cristianoag/minimig/case/Acrylic/minimig_top_engraving.png

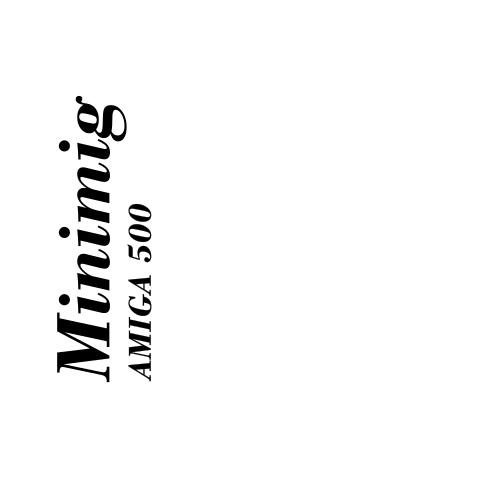
case/Acrylic/minimig_top_engraving.png
