cristianoag/minimig/pictures/20221220_040925518_iOS (Medium).jpg

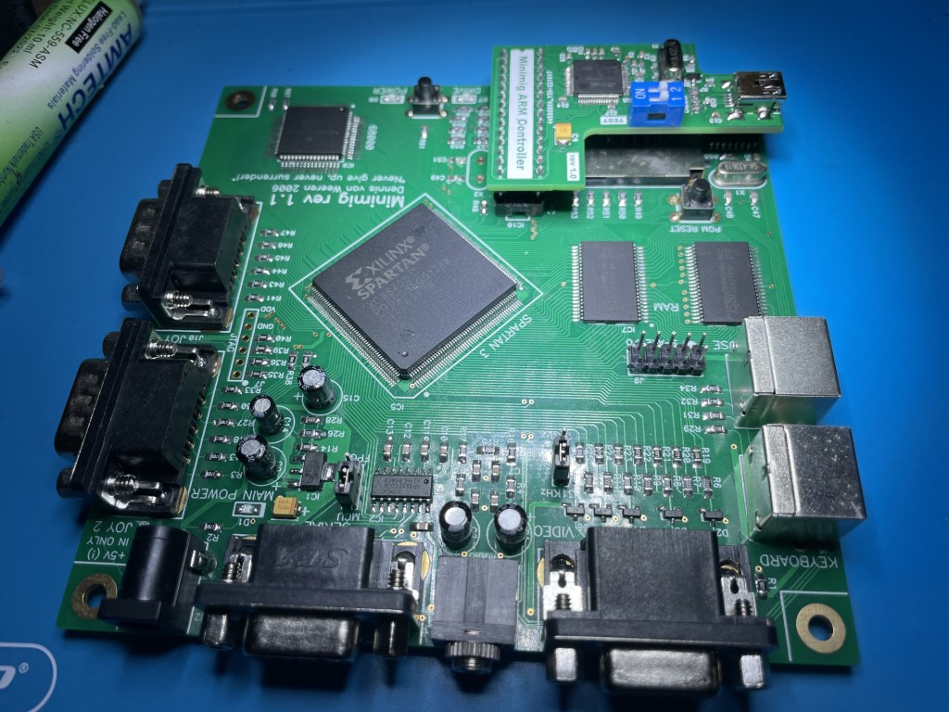
pictures/20221220_040925518_iOS (Medium).jpg
