cristianoag/minimig/pictures/20221222_223349225_iOS.jpg

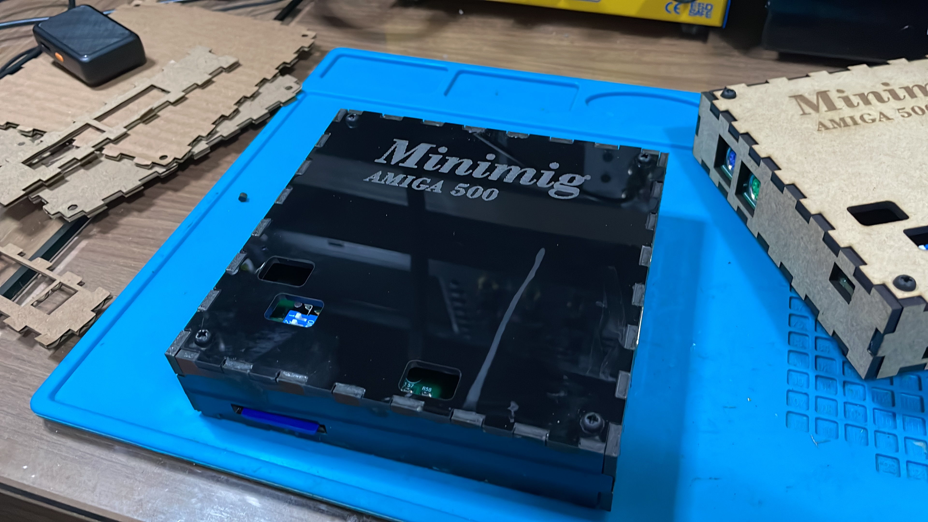
pictures/20221222_223349225_iOS.jpg
