cristianoag/minimig/pictures/20221222_223627648_iOS.jpg

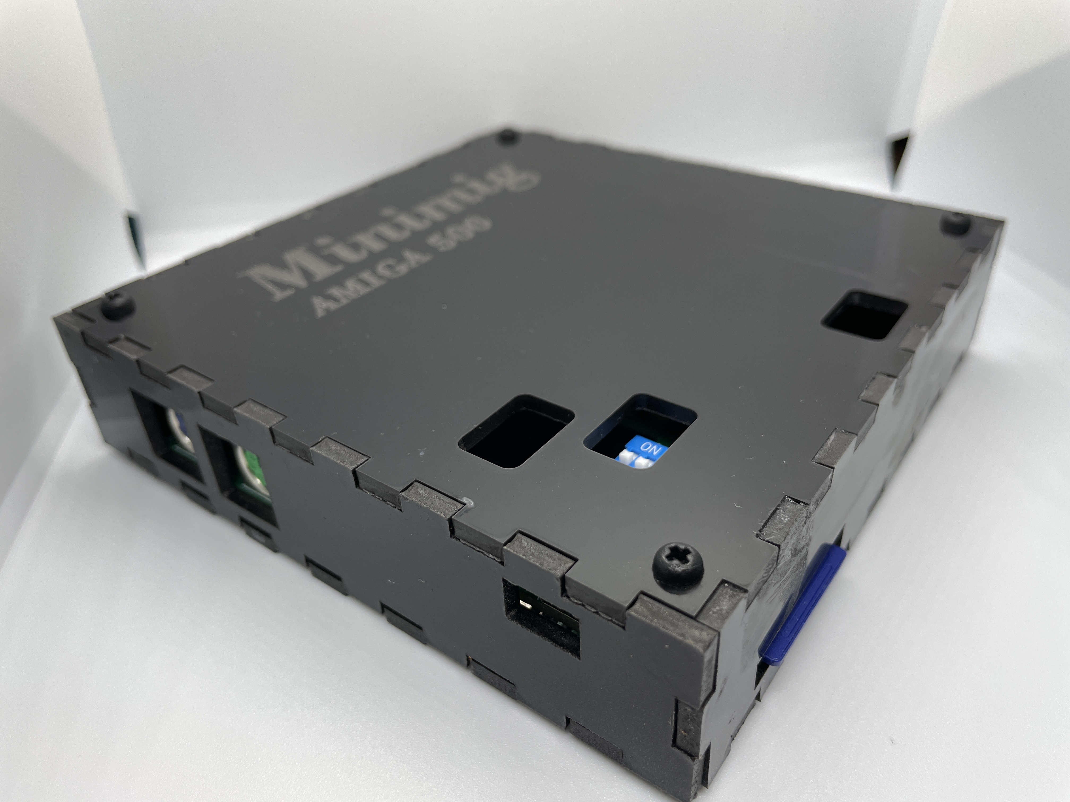
pictures/20221222_223627648_iOS.jpg
