cristianoag/minimig/pictures/20221222_223635217_iOS.jpg

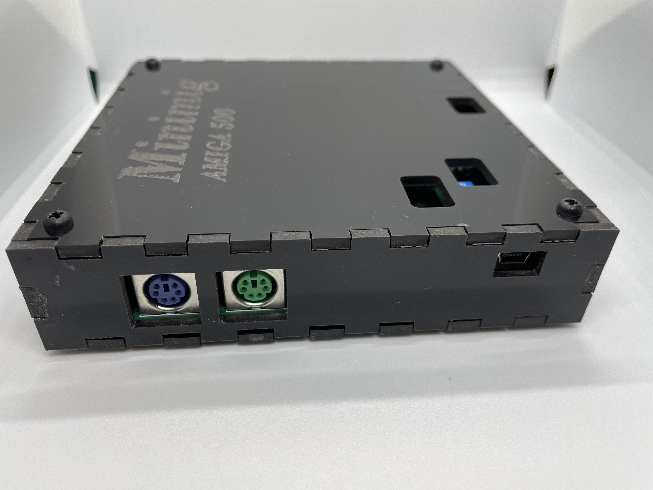
pictures/20221222_223635217_iOS.jpg
