cristianoag/minimig/pictures/20221222_223641382_iOS.jpg

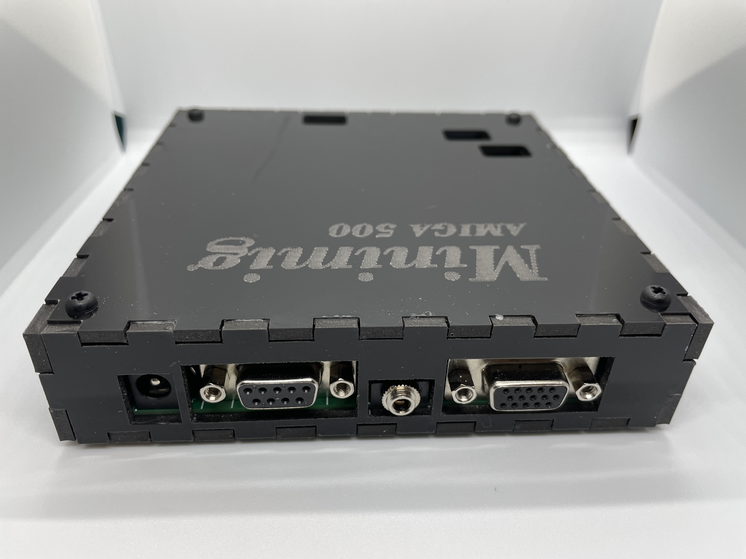
pictures/20221222_223641382_iOS.jpg
