cristianoag/minimig/pictures/20221222_223811196_iOS.jpg

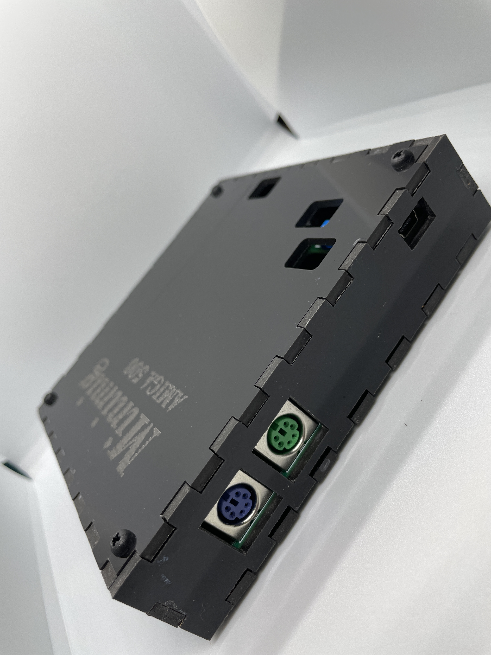
pictures/20221222_223811196_iOS.jpg
