cristianoag/minimig/pictures/20221222_223824692_iOS.jpg

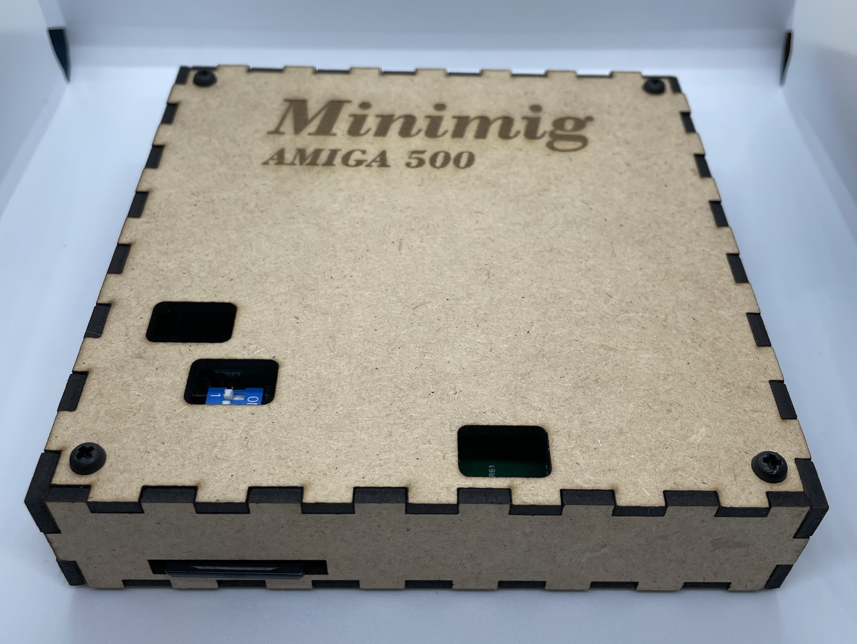
pictures/20221222_223824692_iOS.jpg
