cristianoag/minimig/pictures/20221222_223850903_iOS.jpg

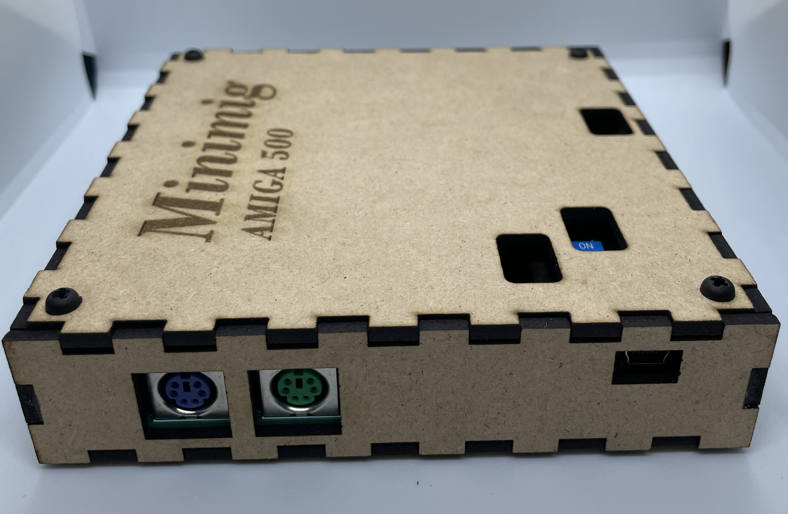
pictures/20221222_223850903_iOS.jpg
