cristianoag/minimig/pictures/20221222_223900050_iOS.jpg

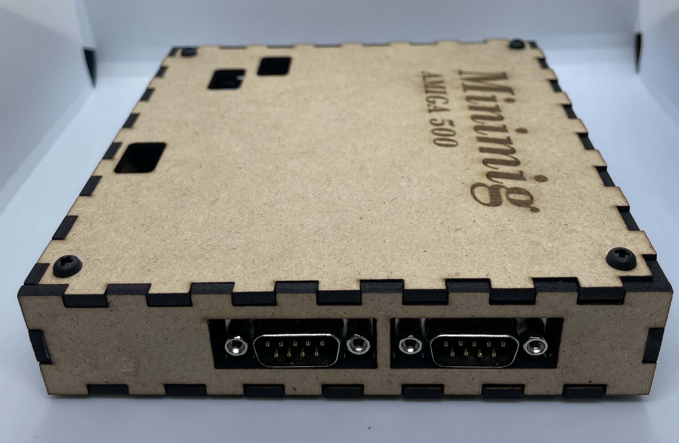
pictures/20221222_223900050_iOS.jpg
