cristianoag/minimig/pictures/20221222_225259371_iOS.jpg

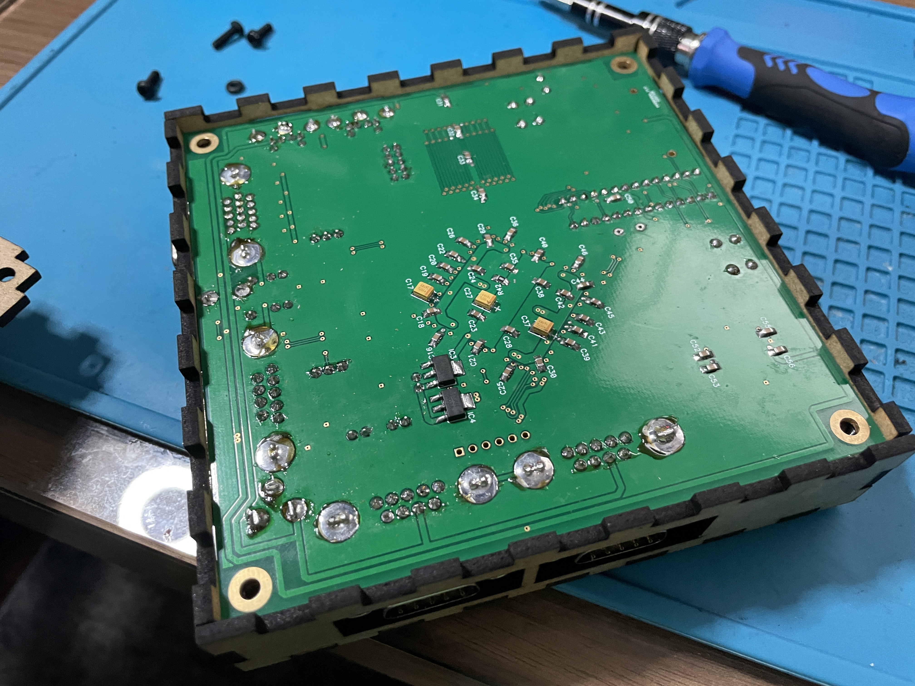
pictures/20221222_225259371_iOS.jpg
