cristianoag/minimig/pictures/20221222_165635106_iOS.jpg

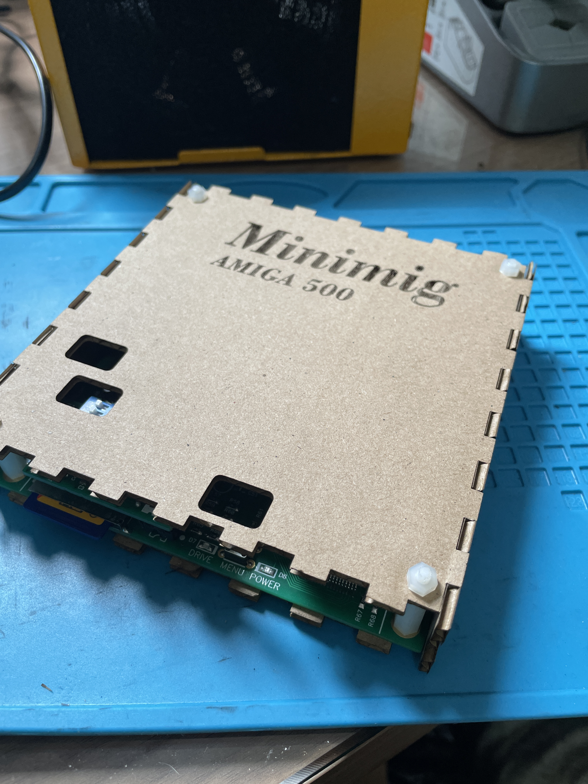
pictures/20221222_165635106_iOS.jpg
